melatova/SaucemakersSentinel/Sentinel_IoT_Device/docs/bitmap_brainstorm.jpg

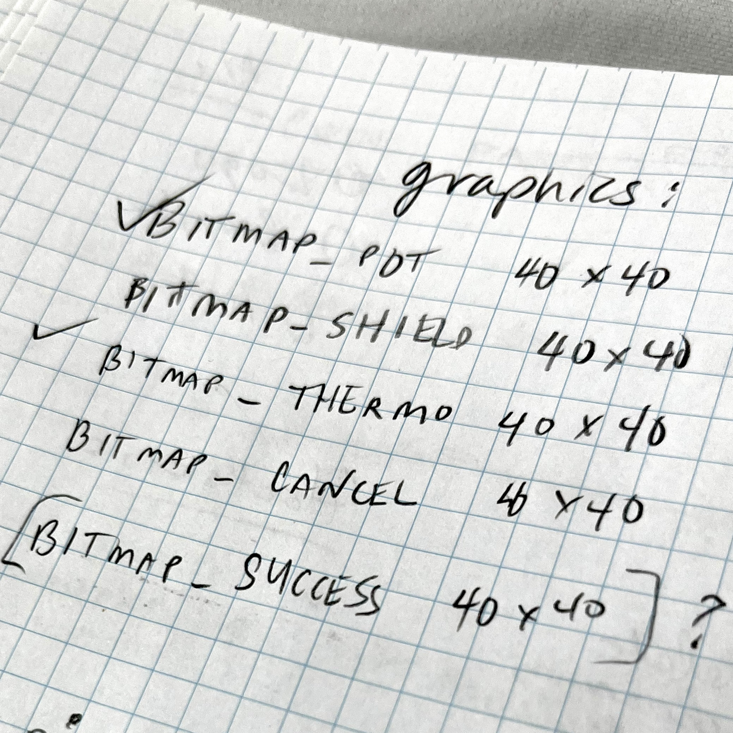
Sentinel_IoT_Device/docs/bitmap_brainstorm.jpg
