melatova/SaucemakersSentinel/Sentinel_IoT_Device/docs/Box_and_therm.jpg

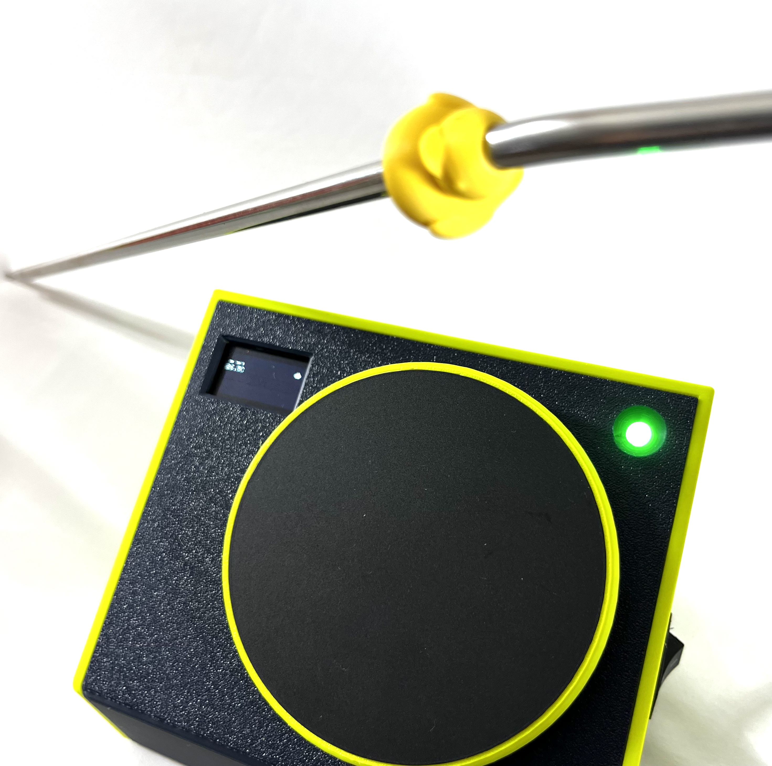
Sentinel_IoT_Device/docs/Box_and_therm.jpg
