melatova/SaucemakersSentinel/Sentinel_IoT_Device/docs/box_back.jpg

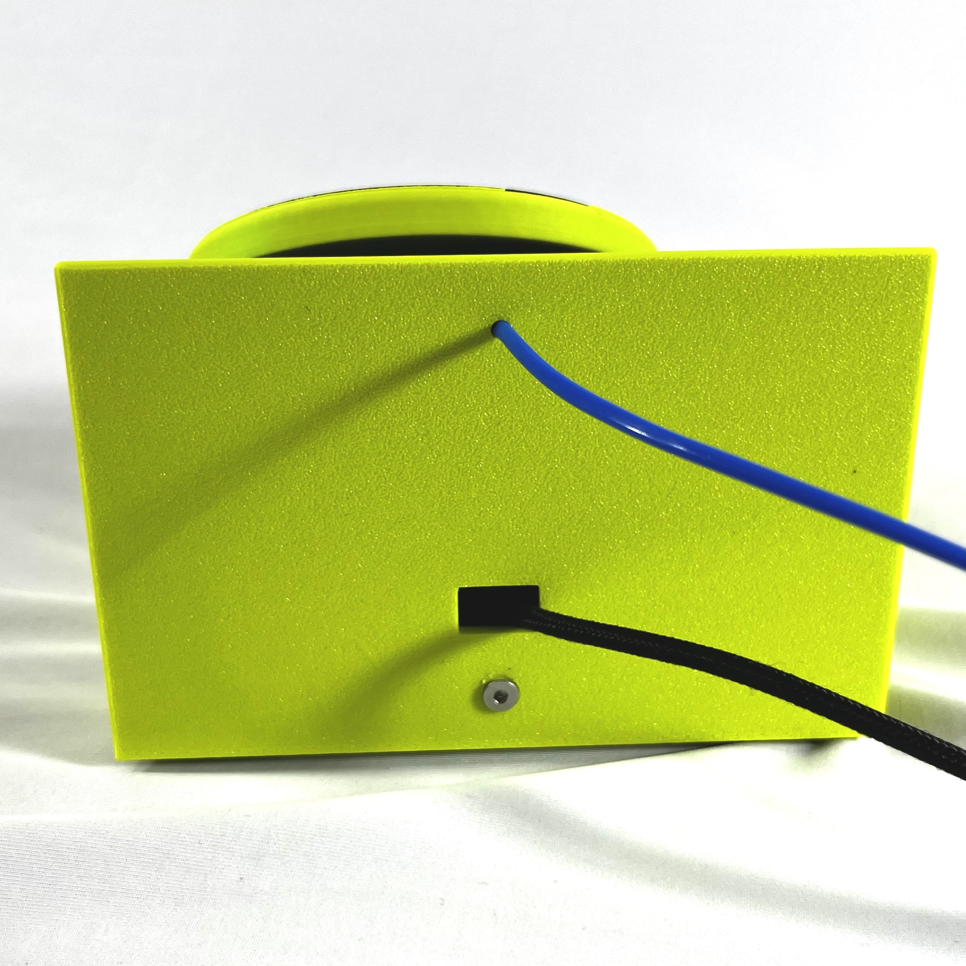
Sentinel_IoT_Device/docs/box_back.jpg
