melatova/SaucemakersSentinel/Sentinel_IoT_Device/docs/box_bottom.jpg

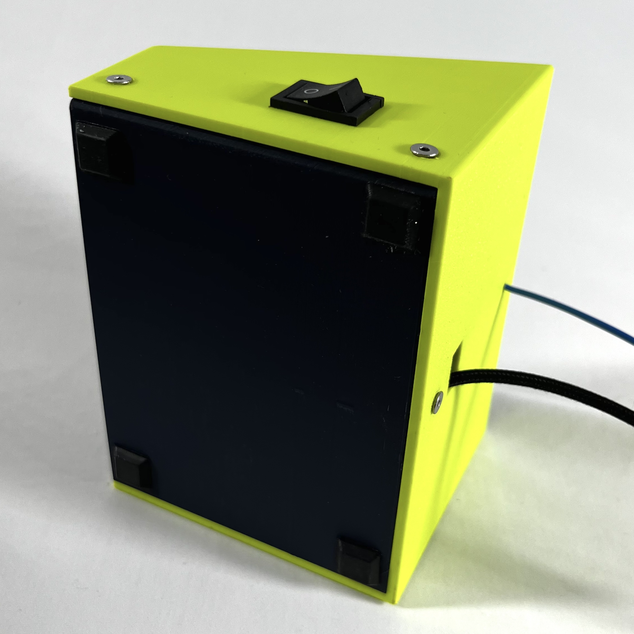
Sentinel_IoT_Device/docs/box_bottom.jpg
