melatova/SaucemakersSentinel/Sentinel_IoT_Device/docs/box_bright_light.jpg

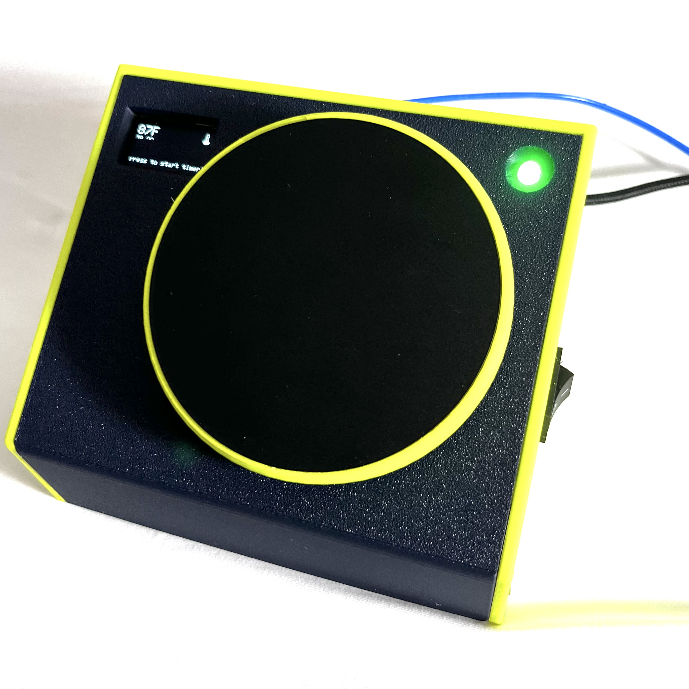
Sentinel_IoT_Device/docs/box_bright_light.jpg
