melatova/SaucemakersSentinel/Sentinel_IoT_Device/docs/box_dimensioned_draft.jpg

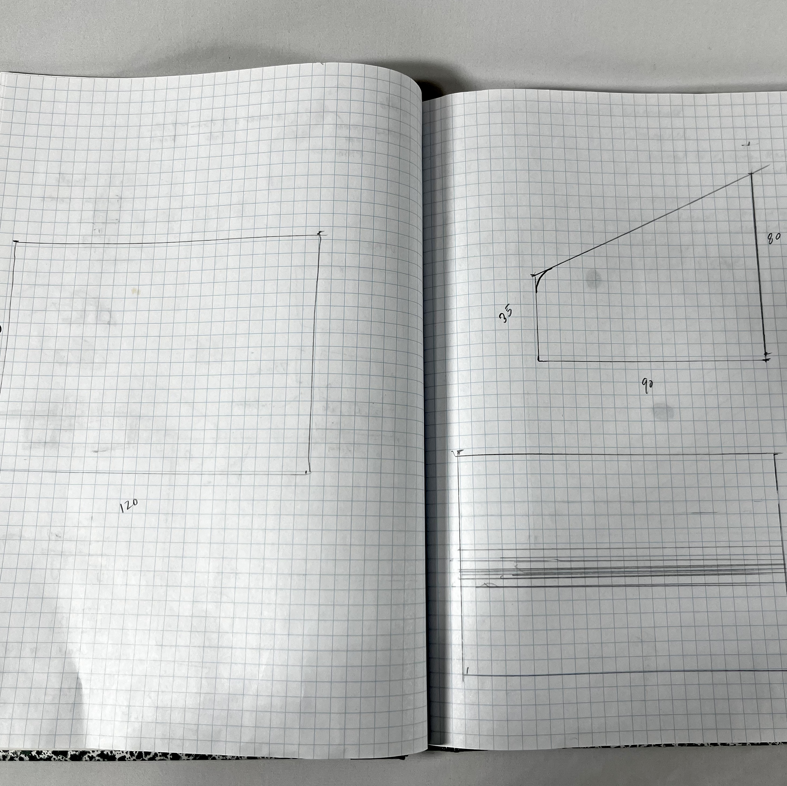
Sentinel_IoT_Device/docs/box_dimensioned_draft.jpg
