melatova/SaucemakersSentinel/Sentinel_IoT_Device/docs/Box_front_cad.png

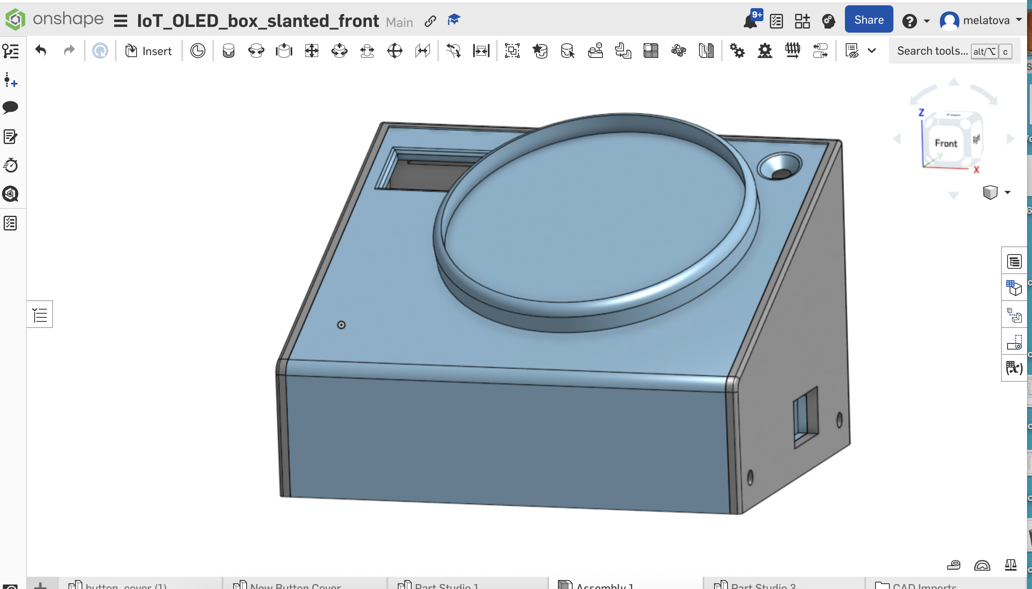
Sentinel_IoT_Device/docs/Box_front_cad.png
