melatova/SaucemakersSentinel/Sentinel_IoT_Device/docs/code_notes_early.jpg

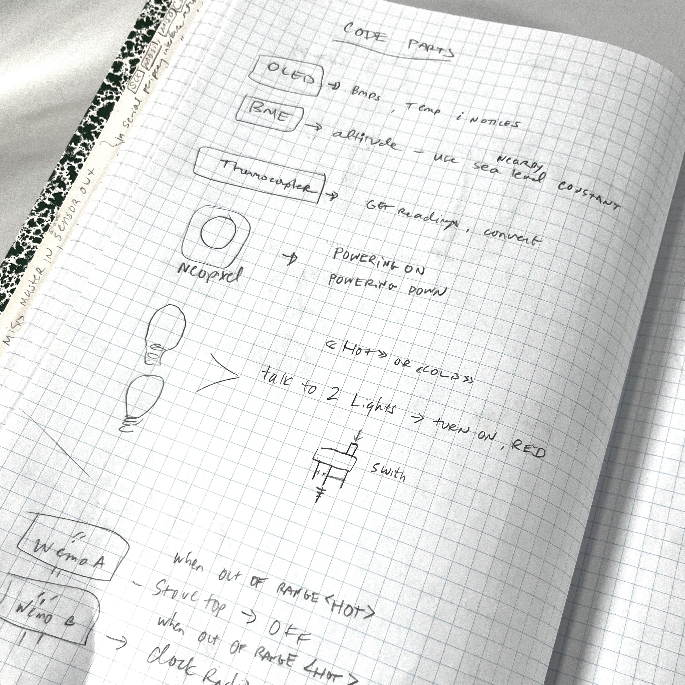
Sentinel_IoT_Device/docs/code_notes_early.jpg
