melatova/SaucemakersSentinel/Sentinel_IoT_Device/docs/sketch_box_front.jpg

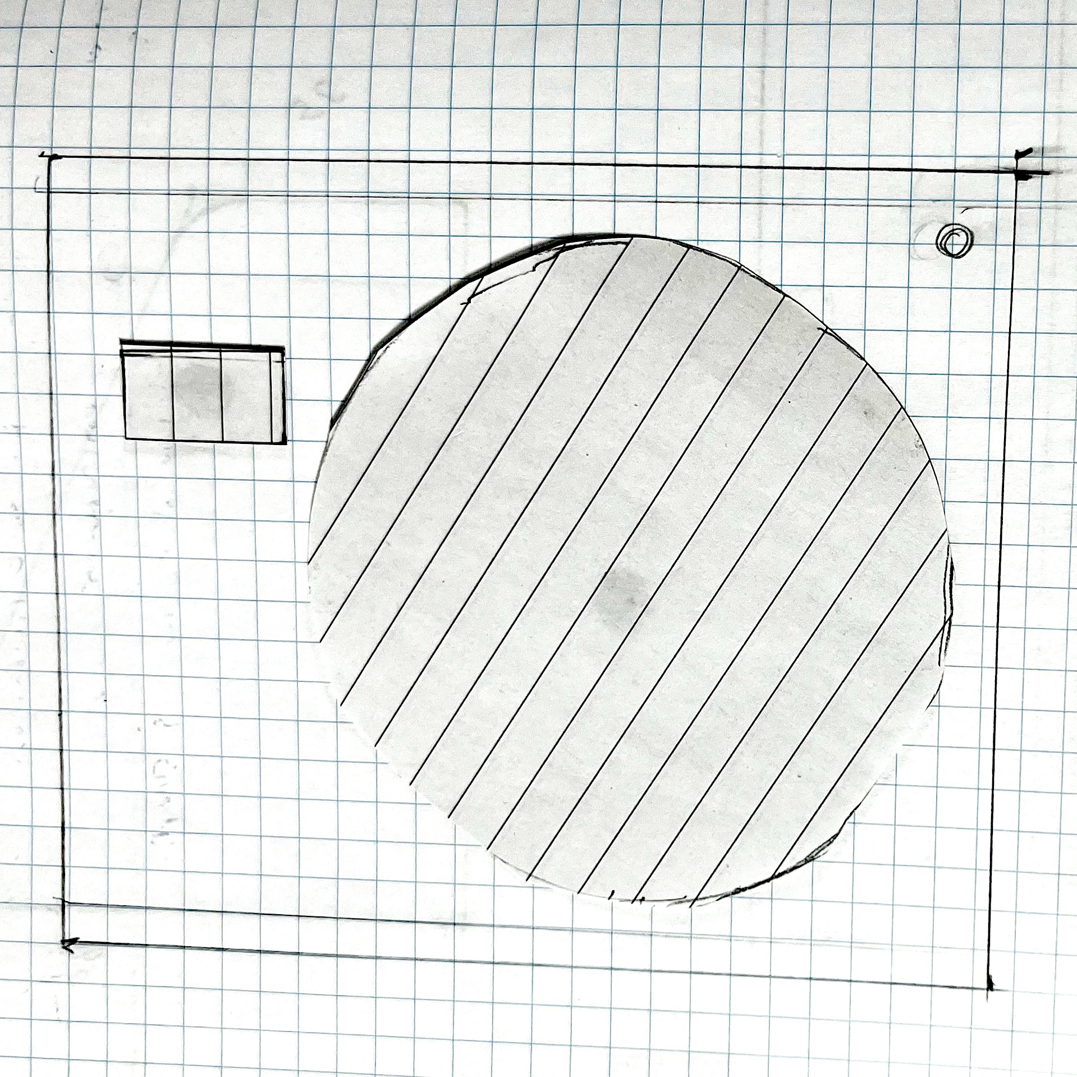
Sentinel_IoT_Device/docs/sketch_box_front.jpg
