melatova/SaucemakersSentinel/Sentinel_IoT_Device/docs/Sketch_OLED_Displays.jpg

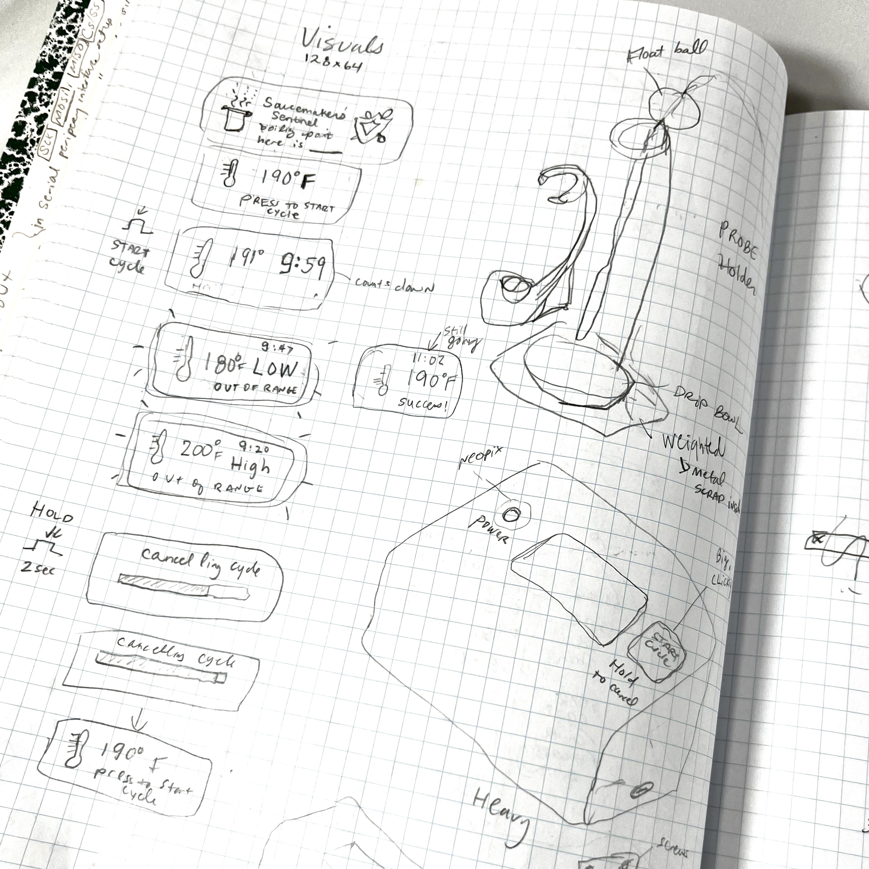
Sentinel_IoT_Device/docs/Sketch_OLED_Displays.jpg
