melatova/SaucemakersSentinel/Sentinel_IoT_Device/docs/sketch_power_button.jpg

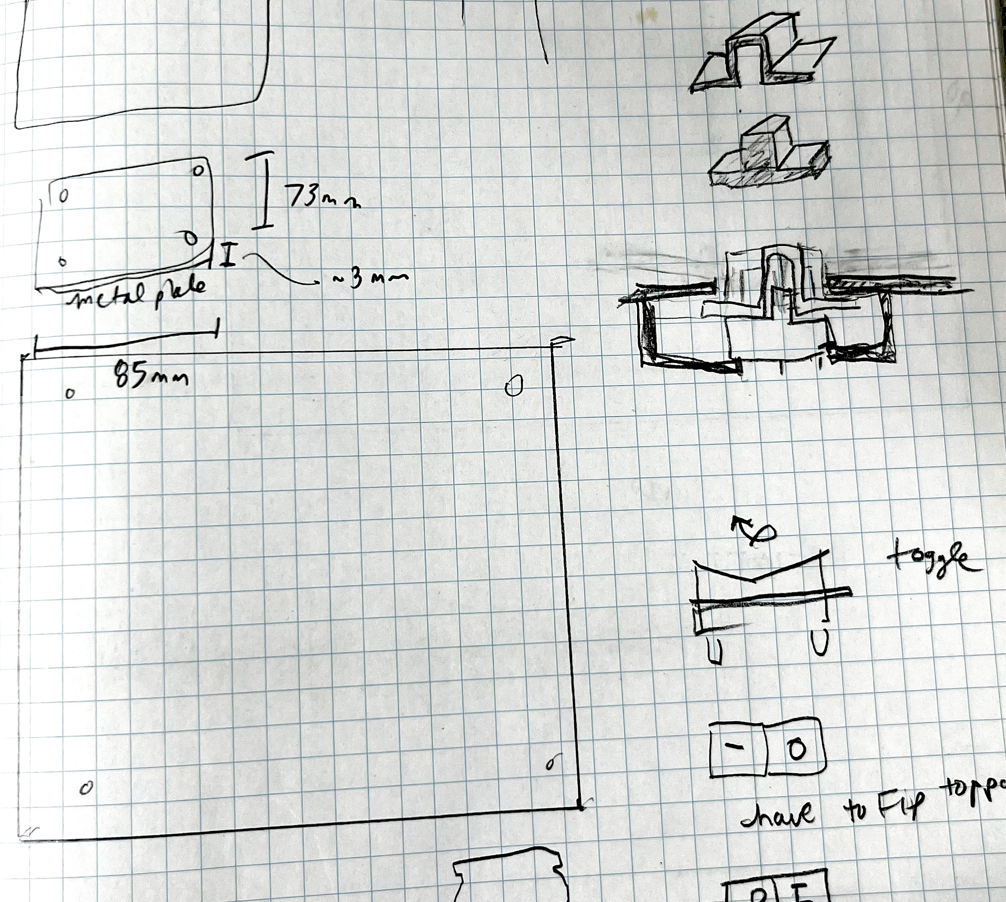
Sentinel_IoT_Device/docs/sketch_power_button.jpg
