melatova/SaucemakersSentinel/Sentinel_IoT_Device/docs/sketch_section_box.jpg

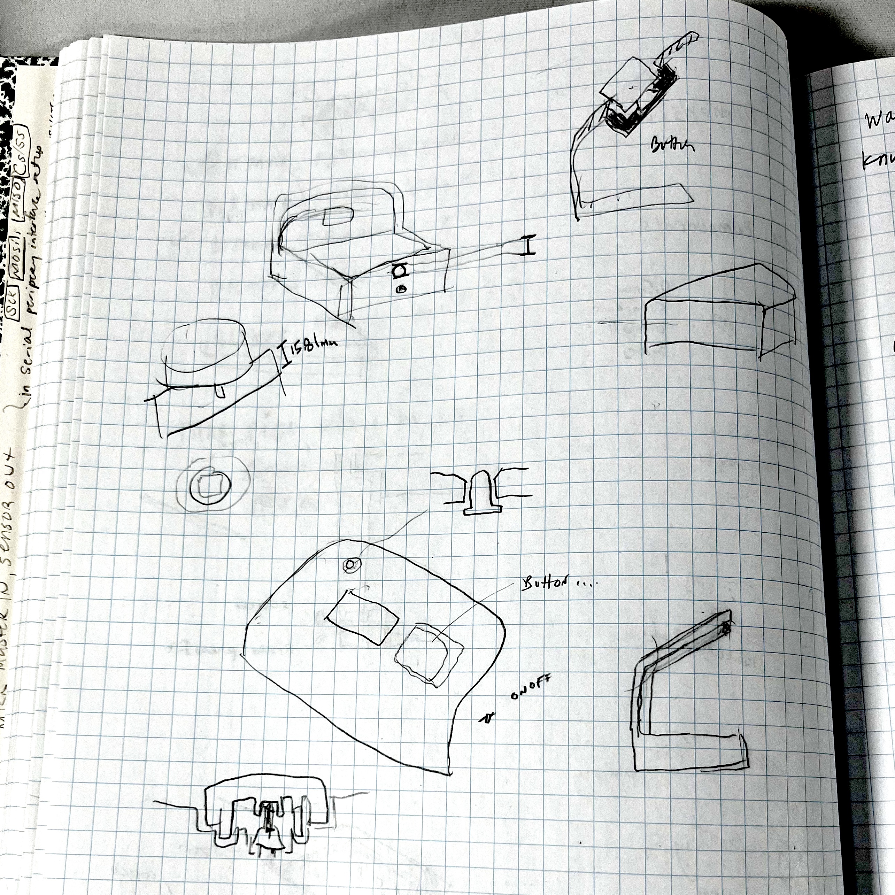
Sentinel_IoT_Device/docs/sketch_section_box.jpg
