melatova/SaucemakersSentinel/Sentinel_IoT_Device/docs/stand_sketches.jpg

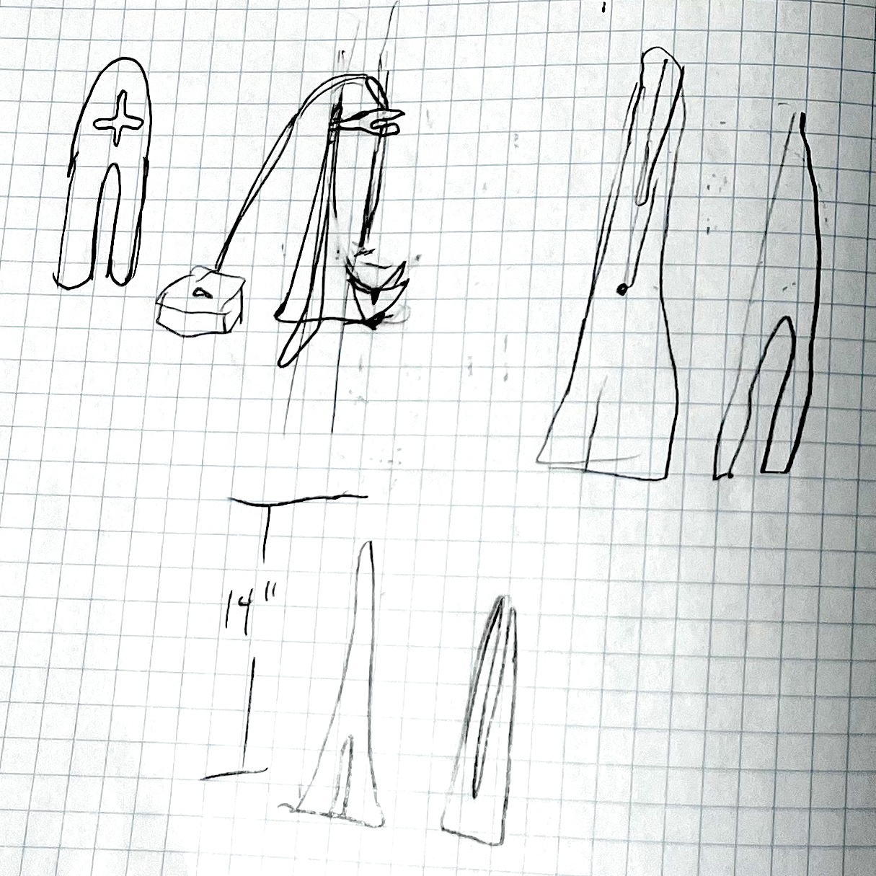
Sentinel_IoT_Device/docs/stand_sketches.jpg
