melatova/SaucemakersSentinel/Sentinel_IoT_Device/docs/Temp_monitor_device_fritzing_bb.png

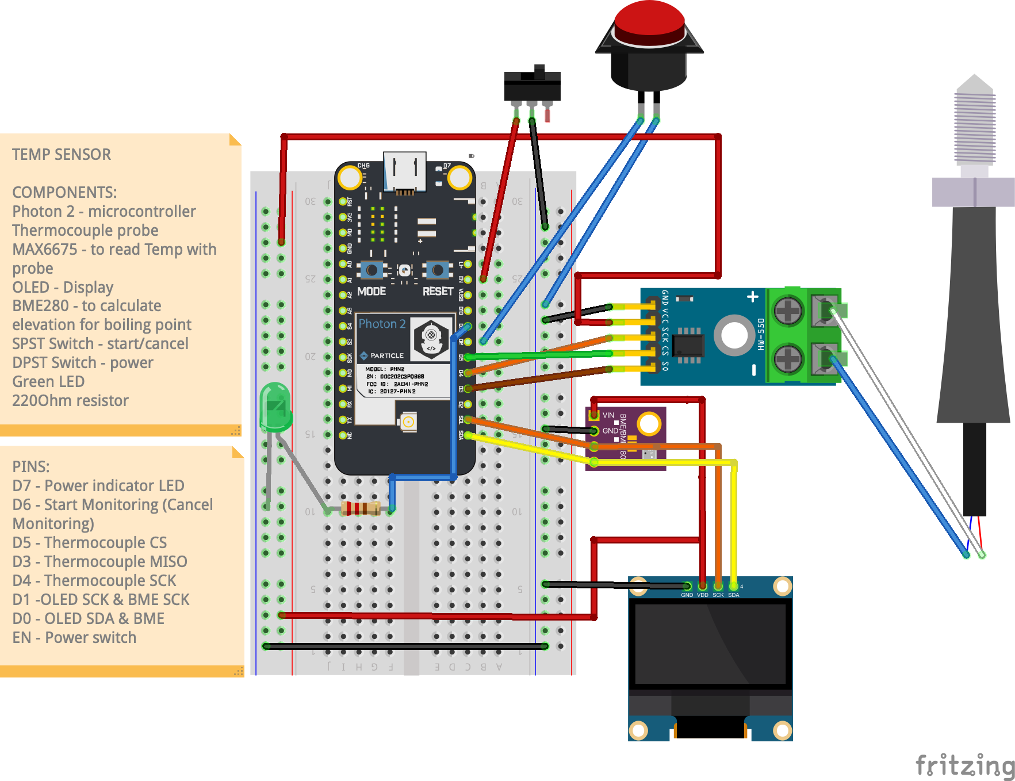
Sentinel_IoT_Device/docs/Temp_monitor_device_fritzing_bb.png
