melatova/SaucemakersSentinel/Sentinel_IoT_Device/docs/Temp_monitor_device_fritzing_schem.png

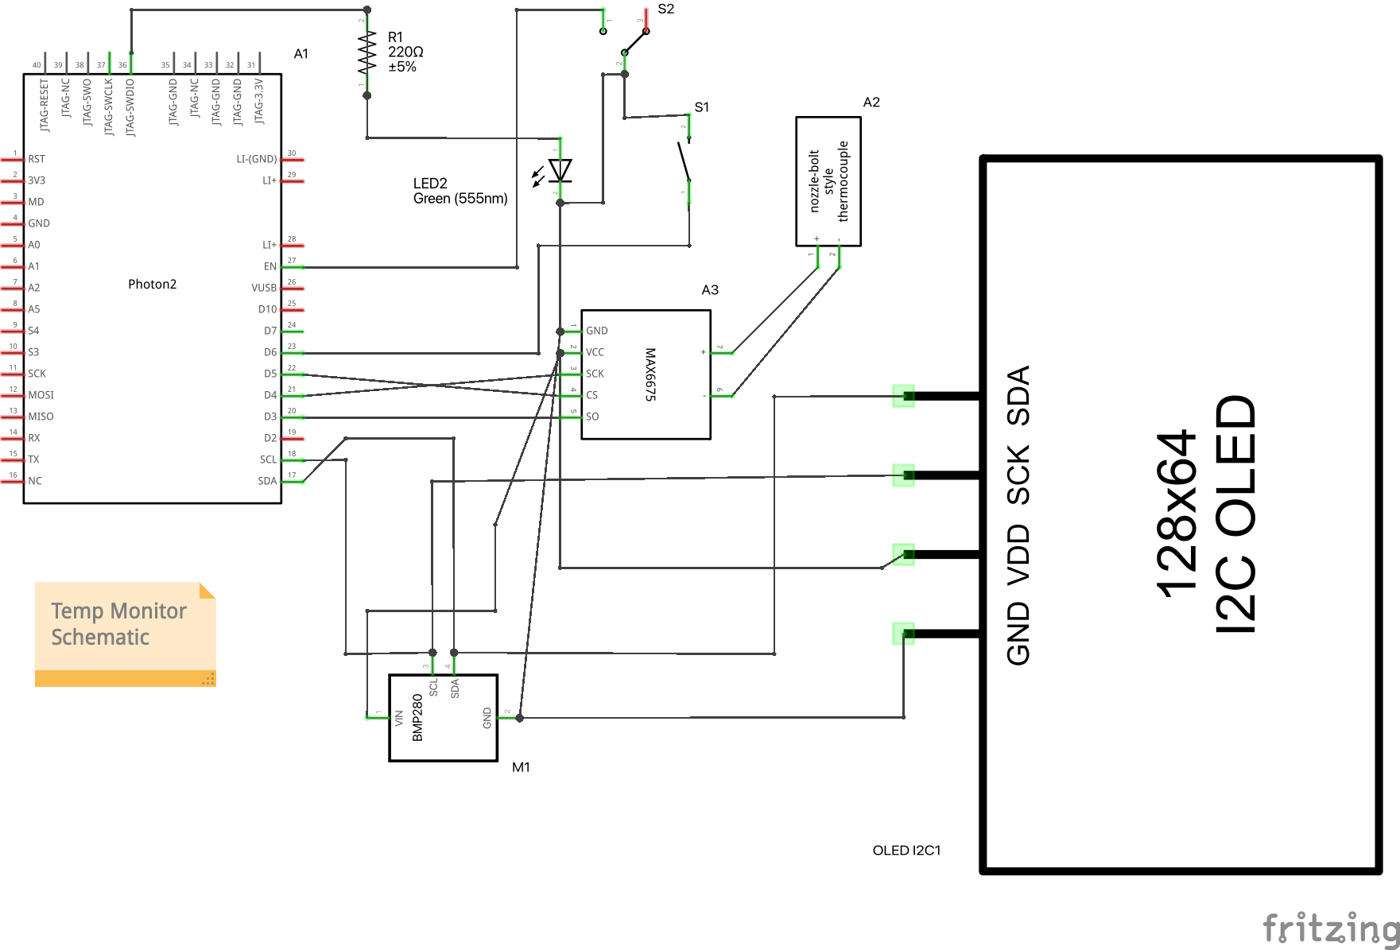
Sentinel_IoT_Device/docs/Temp_monitor_device_fritzing_schem.png
