melatova/SaucemakersSentinel/Sentinel_IoT_Device/images/box_left_side.jpg

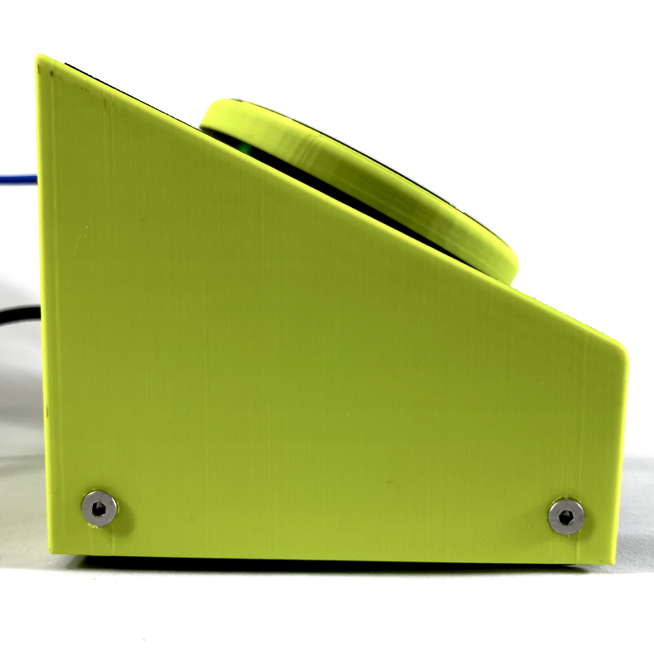
Sentinel_IoT_Device/images/box_left_side.jpg
