melatova/SaucemakersSentinel/Sentinel_IoT_Device/images/Box_section_cad.png

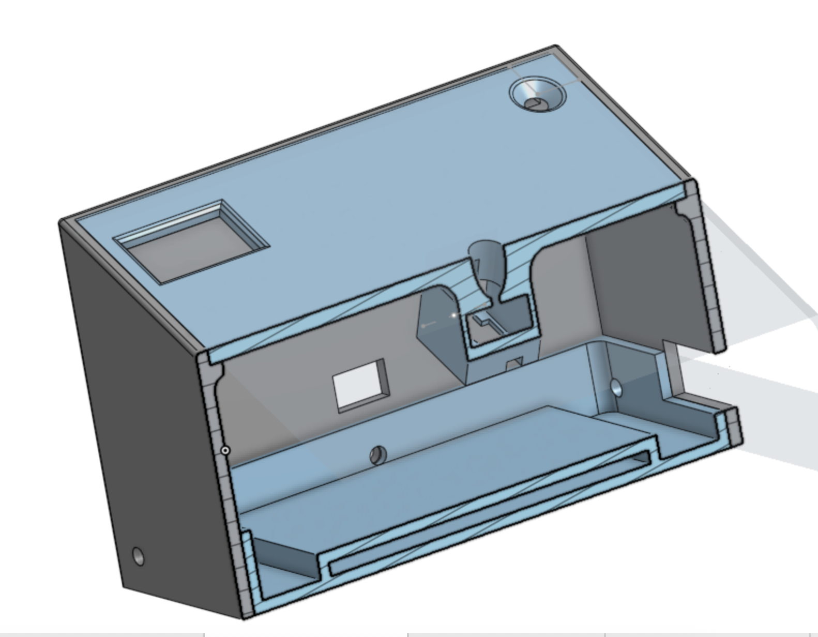
Sentinel_IoT_Device/images/Box_section_cad.png
