melatova/SaucemakersSentinel/Sentinel_IoT_Device/images/Box_section_cad_fullscreen.png

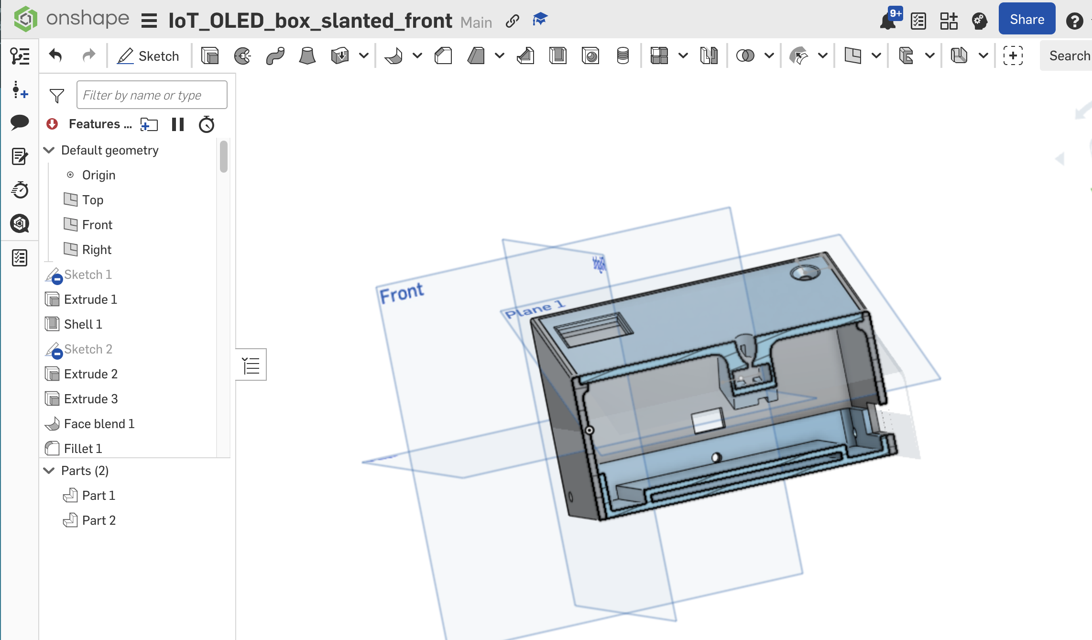
Sentinel_IoT_Device/images/Box_section_cad_fullscreen.png
