melatova/SaucemakersSentinel/Sentinel_IoT_Device/images/Chef.jpg

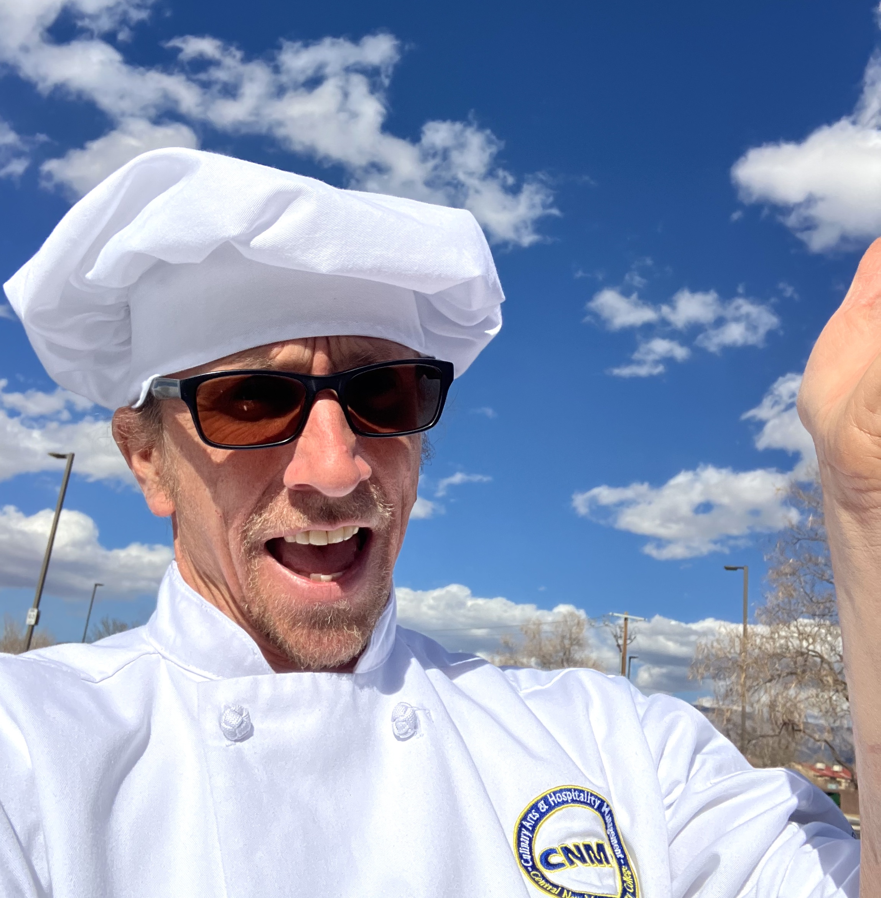
Sentinel_IoT_Device/images/Chef.jpg
