melatova/SaucemakersSentinel/Sentinel_IoT_Device/images/circuitboard2.jpg

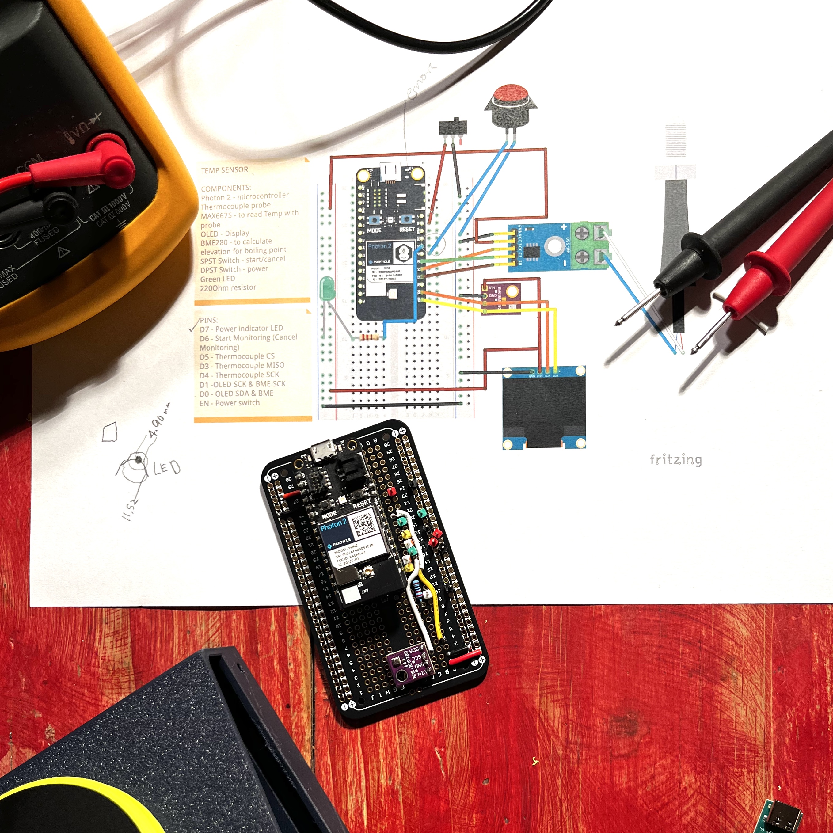
Sentinel_IoT_Device/images/circuitboard2.jpg
