melatova/SaucemakersSentinel/Sentinel_IoT_Device/images/circuitboard.jpg

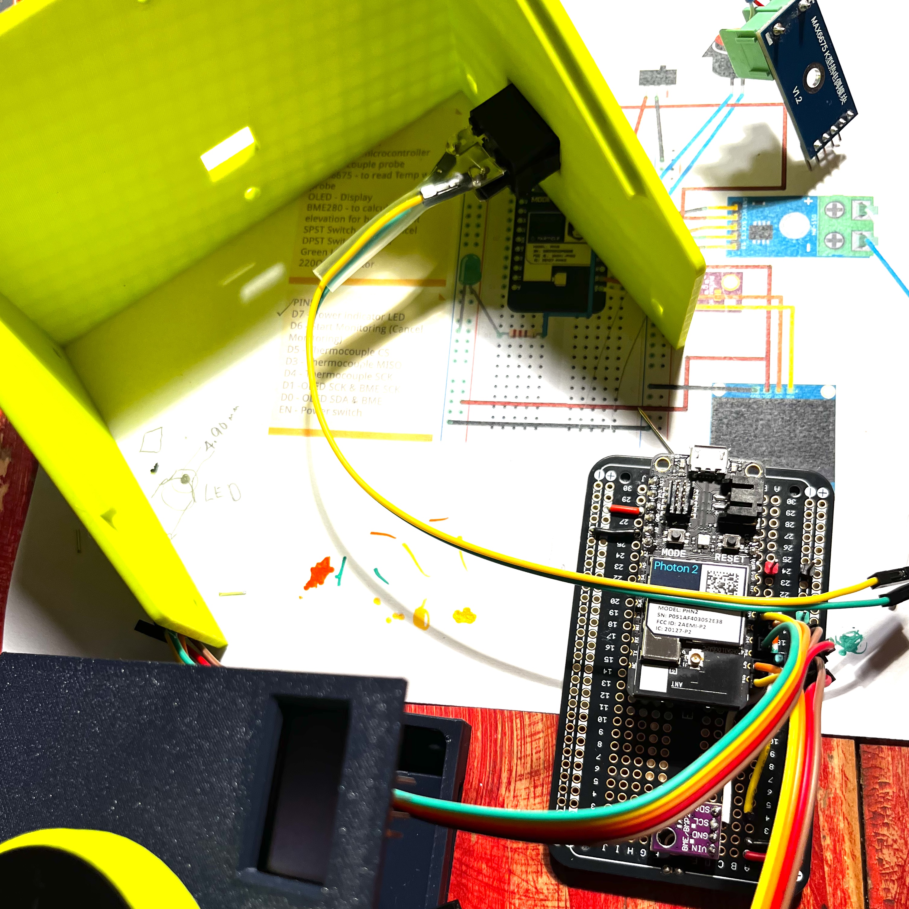
Sentinel_IoT_Device/images/circuitboard.jpg
