melatova/SaucemakersSentinel/Sentinel_IoT_Device/images/device_with_active_screen_front.jpg

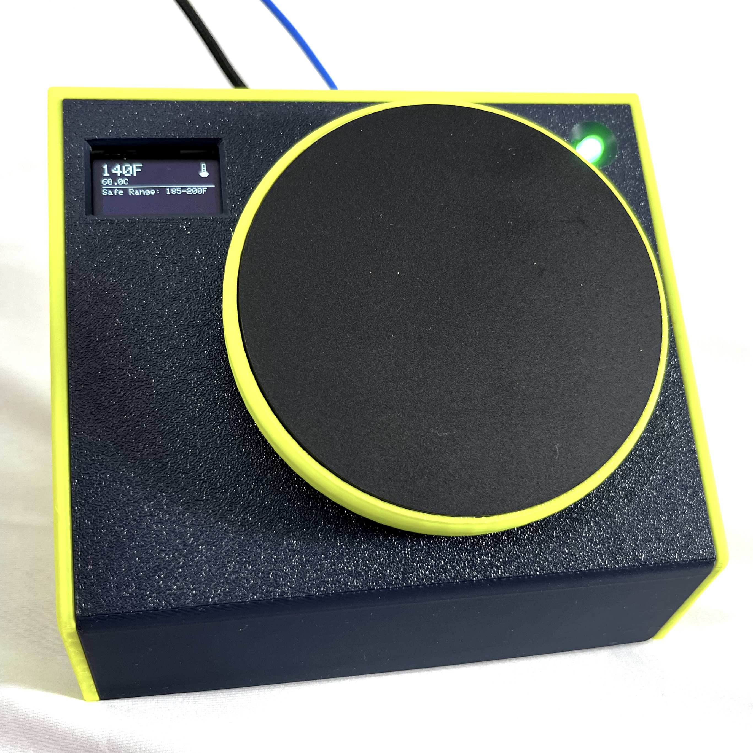
Sentinel_IoT_Device/images/device_with_active_screen_front.jpg
