melatova/SaucemakersSentinel/Sentinel_IoT_Device/images/elbow_hit2.jpg

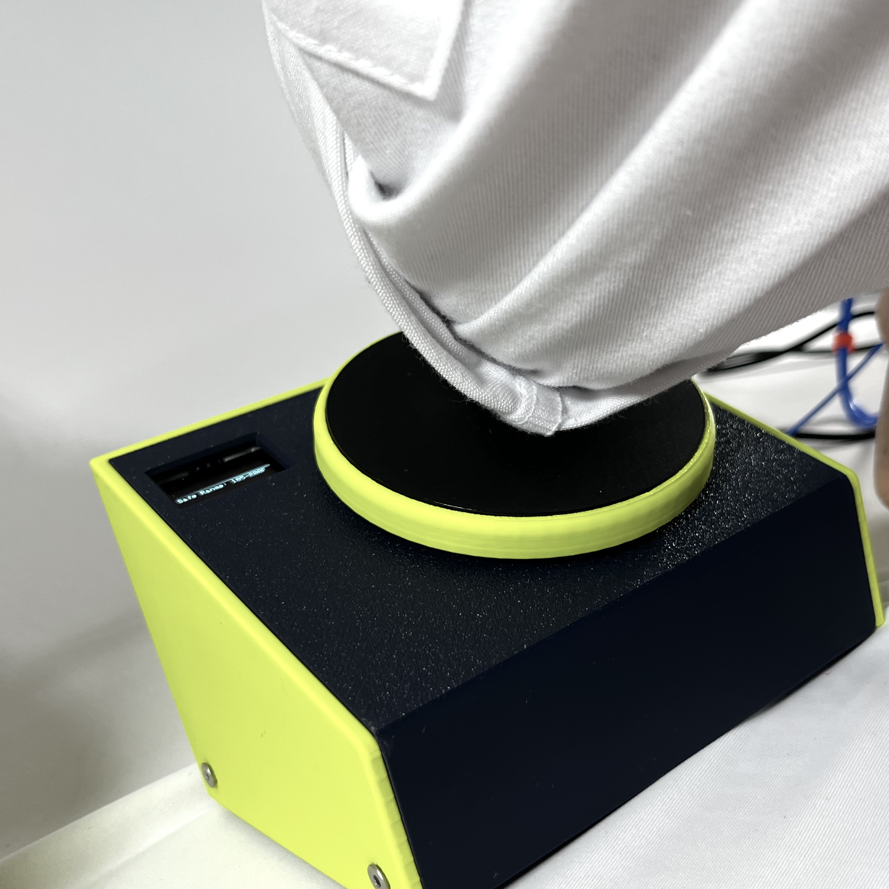
Sentinel_IoT_Device/images/elbow_hit2.jpg
