melatova/SaucemakersSentinel/Sentinel_IoT_Device/images/elbow_hit.jpg

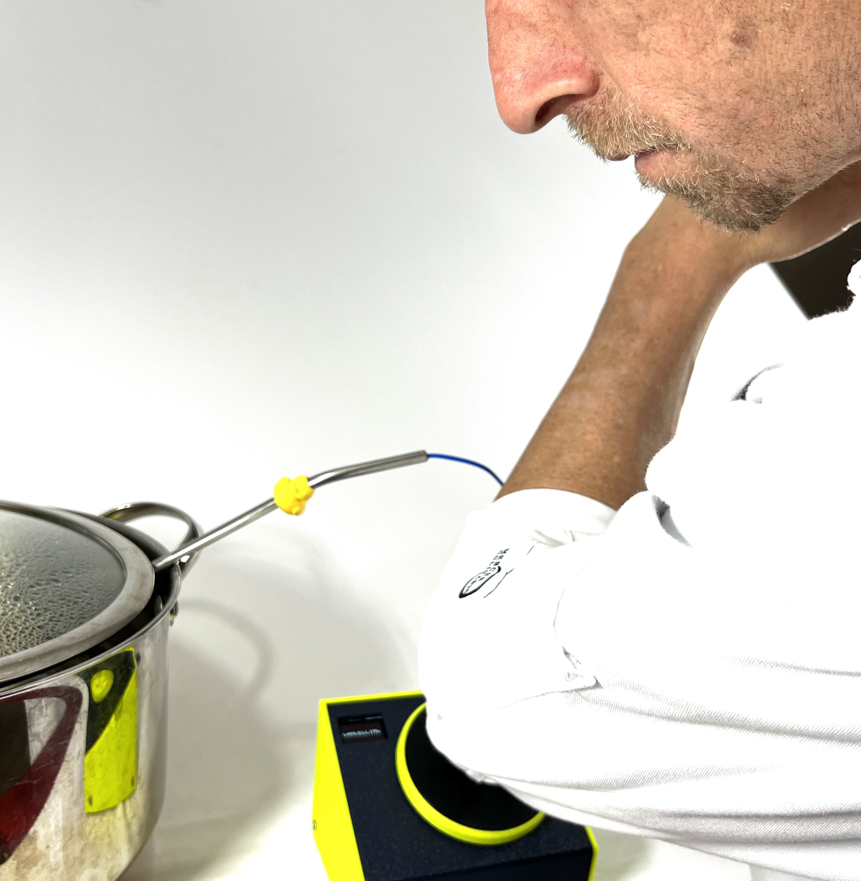
Sentinel_IoT_Device/images/elbow_hit.jpg
