melatova/SaucemakersSentinel/Sentinel_IoT_Device/src/bitmaps.h

/*
 * Project:  Saucier’s Sentinel - Hot Process Timer
 * File:     bitmaps.h  —  pixel art icons for the OLED display
 * Author:   Nicole
 * Date:     03/07/2026
 *
 * Each bitmap is a 2D grid of bits packed into bytes.
 * A 1-bit = white pixel, 0-bit = black (off) pixel.
 * Each row of the image is one horizontal strip of bytes.
 *
 * 16x16 icons: 2 bytes per row x 16 rows = 32 bytes each.
 * 40x40 icons: 5 bytes per row x 40 rows = 200 bytes each.
 *
 * To use a bitmap on the OLED:
 *   display.drawBitmap(x, y, BITMAP_NAME, width, height, WHITE);
 *
 * ── ACTIVE SET (used in the current UI) ─────────────────────────
 *   BITMAP_THERMO16   — thermometer, 16x16 (idle + alert screens)
 *   BITMAP_HOURGLASS16 — hourglass, 16x16  (cycle in progress)
 *   BITMAP_SHIELD16   — shield,    16x16  (unused, archived)
 *   BITMAP_CANCEL16   — circle+X,  16x16  (cancelling screen)
 *   BITMAP_POT        — cooking pot, 40x40 (loading screen)
 *   BITMAP_SHIELD     — detailed shield with checkmark, 40x40 (success)
 *
 * ── ARCHIVE (kept for future use or larger displays) ─────────────
 *   BITMAP_THERMO     — detailed thermometer, 40x40
 *   BITMAP_CANCEL     — detailed cancel swirl, 40x40
 *   BITMAP_SUCCESS    — checkmark in circle,  40x40
 */

#ifndef BITMAPS_H
#define BITMAPS_H

#include "Particle.h"


// ════════════════════════════════════════════════════════════════
//  16x16 ACTIVE ICONS
// ════════════════════════════════════════════════════════════════

// Thermometer — thin tube with tick marks and a round bulb at base.
// Used on: idle screen, too-cold alert (shivers), too-hot alert.
const unsigned char BITMAP_THERMO16[] = {
    0x07,0x80,
    0x04,0x80,
    0x04,0x80,
    0x04,0x80,
    0x04,0x80,
    0x07,0x80,
    0x04,0x80,
    0x04,0x80,
    0x07,0x80,
    0x04,0x80,
    0x07,0xC0,
    0x1F,0xE0,
    0x3F,0xF0,
    0x3F,0xF0,
    0x1F,0xE0,
    0x0F,0xC0
};

// Hourglass — wide top and bottom, pinched to 2px in the middle.
// Used on: cycle-in-progress screen.
const unsigned char BITMAP_HOURGLASS16[] = {
    0x7F,0xFE,
    0x7F,0xFE,
    0x3F,0xFC,
    0x1F,0xF8,
    0x0F,0xF0,
    0x07,0xE0,
    0x03,0xC0,
    0x01,0x80,
    0x03,0xC0,
    0x07,0xE0,
    0x0F,0xF0,
    0x1F,0xF8,
    0x3F,0xFC,
    0x7F,0xFE,
    0x7F,0xFE,
    0x7F,0xFE
};

// Shield — pentagon pointing downward.
// Archived: replaced on success screen by the larger BITMAP_SHIELD (40x40).
const unsigned char BITMAP_SHIELD16[] = {
    0x1F,0xE0,
    0x3F,0xF0,
    0x7F,0xF8,
    0x7F,0xF8,
    0x78,0x78,
    0x7C,0xF8,
    0x7F,0xF8,
    0x3F,0xF0,
    0x3F,0xF0,
    0x1F,0xE0,
    0x0F,0xC0,
    0x07,0x80,
    0x03,0x00,
    0x00,0x00,
    0x00,0x00,
    0x00,0x00
};

// Cancel — circle outline with an X inside.
// Used on: cancelling screen.
// Note: written in binary (B00000000) notation — same result as hex,
// just easier to see the pixel pattern row by row.
const unsigned char BITMAP_CANCEL16[] = {
    B00000000,B00000000,
    B00001111,B11110000,
    B00011111,B11111000,
    B00001000,B00010000,
    B00001100,B00110000,
    B00000110,B01100000,
    B00000011,B11000000,
    B00000011,B11000000,
    B00000011,B11000000,
    B00000011,B11000000,
    B00000111,B11100000,
    B00001111,B11110000,
    B00001111,B11110000,
    B00011111,B11111000,
    B00001111,B11110000,
    B00000000,B00000000
};


// ════════════════════════════════════════════════════════════════
//  40x40 ICONS  (active)
// ════════════════════════════════════════════════════════════════

// Cooking pot — shown on the loading screen while the device warms up.
// Steam animation is drawn separately in code (animated pixel puffs).
const unsigned char BITMAP_POT[] = {
    0x00,0x00,0x18,0x00,0x00,
    0x00,0x00,0x1C,0x00,0x00,
    0x00,0x00,0x1C,0x00,0x00,
    0x00,0x06,0x1C,0x60,0x00,
    0x00,0x07,0x1C,0xE0,0x00,
    0x00,0x07,0x1C,0x70,0x00,
    0x00,0x07,0x3C,0x70,0x00,
    0x00,0x07,0x38,0x70,0x00,
    0x00,0x0F,0x38,0xE0,0x00,
    0x00,0x0E,0x38,0xE0,0x00,
    0x00,0x0E,0x38,0xE0,0x00,
    0x00,0x0F,0x38,0xE0,0x00,
    0x00,0x06,0x18,0x60,0x00,
    0x00,0x00,0x00,0x00,0x00,
    0x00,0x00,0x00,0x00,0x00,
    0x03,0xFF,0xFF,0xFF,0xC0,
    0x07,0xFF,0xFF,0xFF,0xE0,
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
    0x03,0xE0,0x07,0xC0,0x00,
    0x01,0xF0,0x0F,0x80,0x00,
    0x00,0xFF,0xFF,0x00,0x00,
    0x00,0x7F,0xFE,0x00,0x00,
    0x00,0x3F,0xFC,0x00,0x00,
    0x00,0x1F,0xF8,0x00,0x00,
    0x00,0x07,0xE0,0x00,0x00,
    0x00,0x01,0x80,0x00,0x00,
    0x00,0x00,0x00,0x00,0x00
};

#endif // BITMAPS_H
